ptravnik/Chording_Keyboards/Pictures/01_Boards_New.jpg

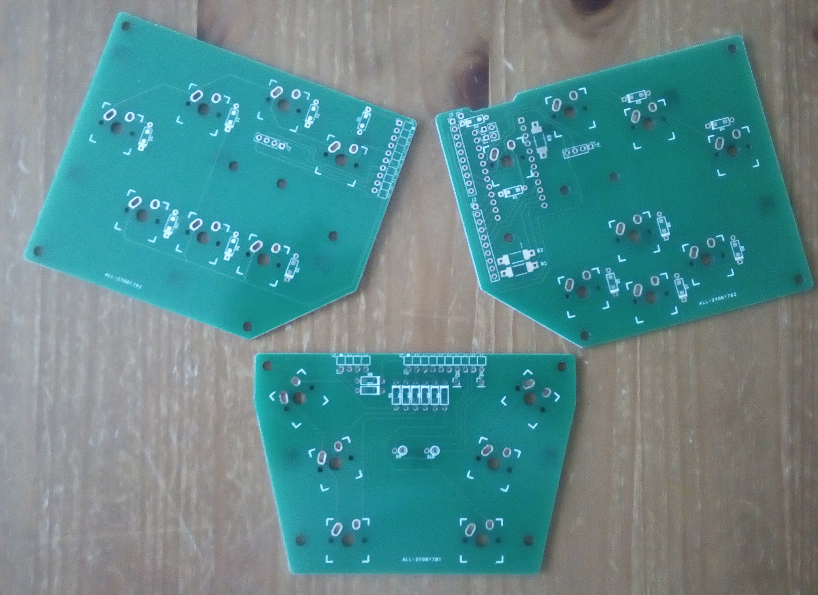
Pictures/01_Boards_New.jpg
