ptravnik/Chording_Keyboards/Pictures/05_Top_View.jpg

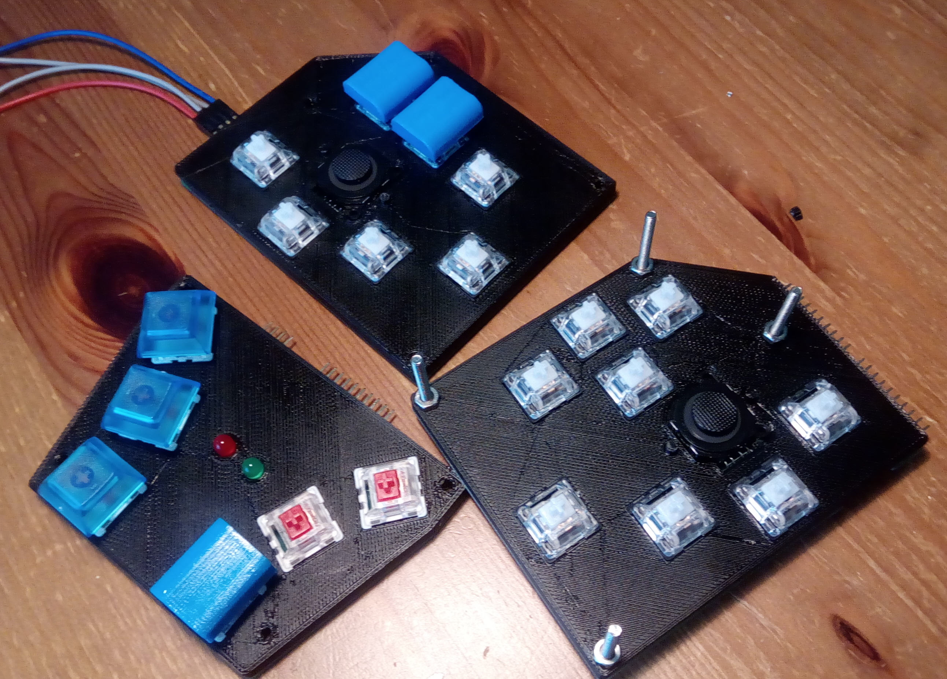
Pictures/05_Top_View.jpg
