ptravnik/Chording_Keyboards/Pictures/06_Joystick_Holder.jpg

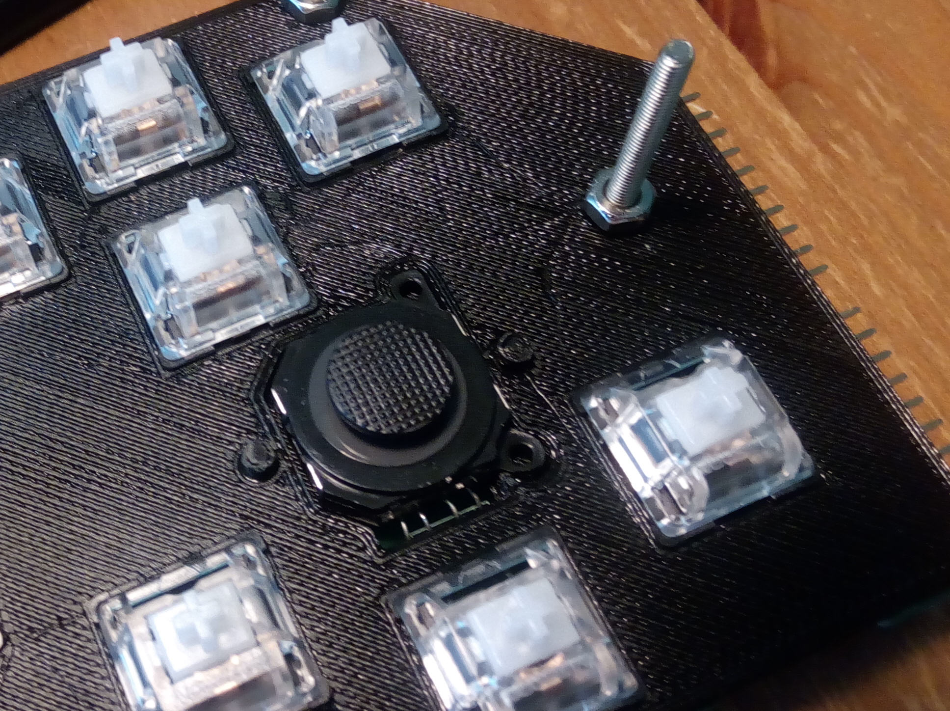
Pictures/06_Joystick_Holder.jpg
