ptravnik/Chording_Keyboards/Pictures/07_Keyboard_Prototype.jpg

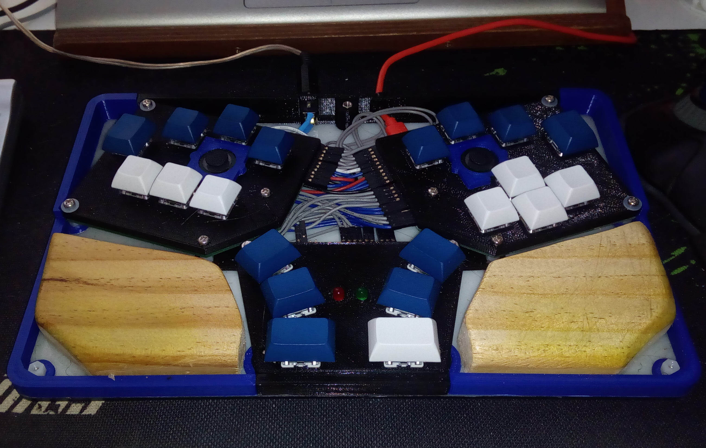
Pictures/07_Keyboard_Prototype.jpg
