ptravnik/Chording_Keyboards/sketch_keyjoy_mark9/keys.h

#define _CH0 (char)0
#define _CPS (char)0xC1
#define _F01 (char)0xC2
#define _F02 (char)0xC3
#define _F03 (char)0xC4
#define _F04 (char)0xC5
#define _F05 (char)0xC6
#define _F06 (char)0xC7
#define _F07 (char)0xC8
#define _F08 (char)0xC9
#define _F09 (char)0xCA
#define _F10 (char)0xCB
#define _F11 (char)0xCC
#define _F12 (char)0xCD
#define _PRN (char)0xCE
#define _TAB (char)0xB3
#define _RTN (char)0xB0
#define _ESC (char)0xB1
#define _INS (char)0xD1
#define _DEL (char)0xD4
#define _PUP (char)0xD3
#define _PDN (char)0xD6
#define _HOM (char)0xD2
#define _END (char)0xD5
#define _BSP (char)0xB2

#define _UP (char)0xDA
#define _DOWN (char)0xD9
#define _LEFT (char)0xD8
#define _RIGHT (char)0xD7

#define _CTRL (char)0x80
#define _SHIFT (char)0x81
#define _ALT (char)0x82
#define _GUI (char)0x83
#define _CTRL_R (char)0x84
#define _SHIFT_R (char)0x85
#define _ALT_R (char)0x86
#define _RIGHT_R (char)0x87

#define _MOUSE_DECIMATOR 5
#define _SCROLL_DELAY1 50
#define _SCROLL_DELAY4 200
#define _NULLMOUSE (signed char)0
#define _MINUSMOUSE (signed char)(-1)
#define _PLUSMOUSE (signed char)1
#define _BLINK_PERIOD 250
#define _SHIFT_RELEASE_TIME 250
