ptravnik/Chording_Keyboards/sketch_keyjoy_mark9/macros.h

// fill here your macros
#define _MACRO_1 "TypeYourMacroHere"
#define _MACRO_2 "TypeYourMacroHere"
#define _MACRO_3 "TypeYourMacroHere"
#define _MACRO_4 "TypeYourMacroHere"
#define _MACRO_5 "TypeYourMacroHere"
#define _MACRO_6 "TypeYourMacroHere"
#define _MACRO_7 "TypeYourMacroHere"
#define _MACRO_8 "TypeYourMacroHere"
#define _MACRO_9 "TypeYourMacroHere"
#define _MACRO_10 "TypeYourMacroHere"
#define _MACRO_11 "TypeYourMacroHere"
#define _MACRO_12 "TypeYourMacroHere"
#define _MACRO_13 "TypeYourMacroHere"
#define _MACRO_14 "TypeYourMacroHere"
#define _MACRO_15 "TypeYourMacroHere"
